KjernNo/specter/hardware/SPECTER.kicad_sch

## KiCad design hardware/SPECTER.kicad_sch (2026-04-02)

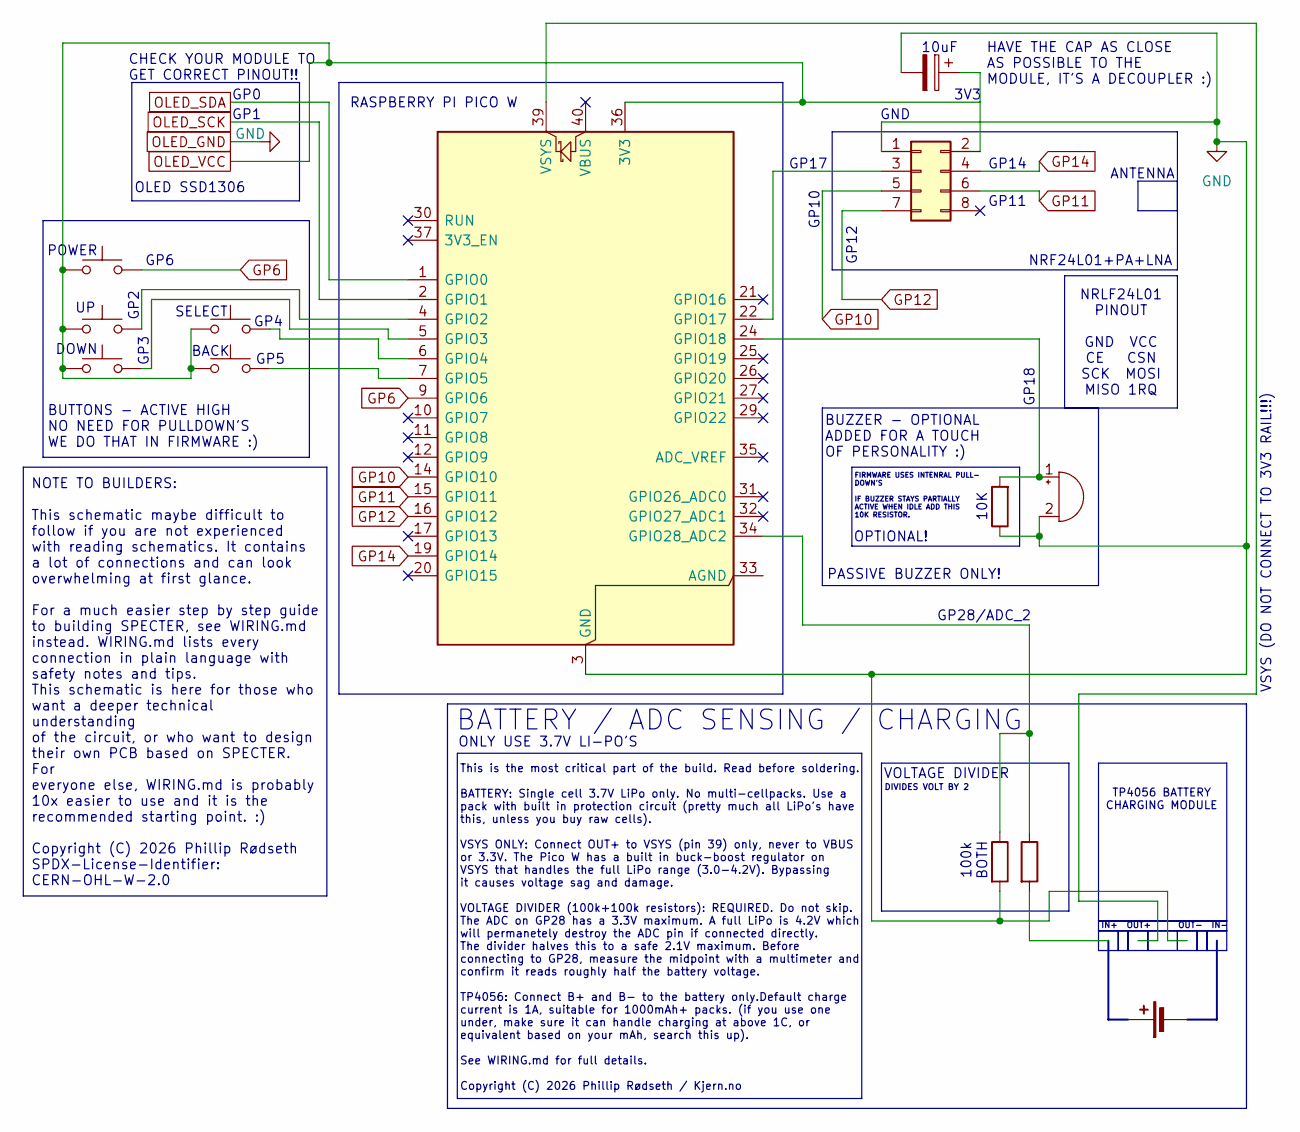
[picture p2: schematic SPECTER.kicad_sch]

Parts:
A1: RaspberryPi_Pico_W; RaspberryPi_Pico_W_SMD_HandSolder
BT1: Battery_Cell
BZ1: Buzzer
C1: C_Polarized
J1: Conn_02x04_Odd_Even
R1, R2, R3: R
SW1, SW2, SW3, SW4, SW5: SW_Push

Connections:
GND: A1.3 (GND), A1.8 (GND), A1.13 (GND), A1.18 (GND), A1.23 (GND), A1.28 (GND), A1.38 (GND), BZ1.2 (-), C1.2, J1.1, R1.1, R3.2
GP6: A1.9 (GPIO6), SW5.2
GP10: A1.14 (GPIO10), J1.5
GP11: A1.15 (GPIO11), J1.6
GP12: A1.16 (GPIO12), J1.7
GP14: A1.19 (GPIO14), J1.4
unnamed: A1.4 (GPIO2), SW3.2
unnamed: A1.5 (GPIO3), SW4.2
unnamed: A1.6 (GPIO4), SW1.2
unnamed: A1.7 (GPIO5), SW2.2
unnamed: A1.22 (GPIO17), J1.3
unnamed: A1.24 (GPIO18), BZ1.1 (+), R1.2
unnamed: A1.34 (GPIO28_ADC2), R2.1, R3.1
OLED_SCK: A1.2 (GPIO1)
OLED_SDA: A1.1 (GPIO0)
OLED_VCC: A1.36 (3V3), C1.1, J1.2, SW1.1, SW2.1, SW3.1, SW4.1, SW5.1

Notes on the sheet:
ANTENNA
VOLTAGE DIVIDER
OLED SSD1306
GP14
GP2
GP18
10uF
HAVE THE CAP AS CLOSE AS POSSIBLE TO THE MODULE, IT'S A DECOUPLER :)
DIVIDES VOLT BY 2
FIRMWARE USES INTENRAL PULL- DOWN'S IF BUZZER STAYS PARTIALLY ACTIVE WHEN IDLE ADD THIS 10K RESISTOR.
PASSIVE BUZZER ONLY!
RASPBERRY PI PICO W
BUTTONS - ACTIVE HIGH NO NEED FOR PULLDOWN'S WE DO THAT IN FIRMWARE :)
GP28/ADC_2
OPTIONAL!
GP1
GP5
This is the most critical part of the build. Read before soldering. BATTERY: Single cell 3.7V LiPo only. No multi-cellpacks. Use a pack with built in protection circuit (pretty much all LiPo's have this, unless you buy raw cells). VSYS ONLY: Connect OUT+ to VSYS (pin 39) only, never to VBUS or 3.3V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
100k BOTH
BATTERY / ADC SENSING / CHARGING
CHECK YOUR MODULE TO GET CORRECT PINOUT!!
VSYS (DO NOT CONNECT TO 3V3 RAIL!!!)
BACK
GP12
GP11
GP6
ONLY USE 3.7V LI-PO'S
GND
GP10
GP0
3V3
GP4
IN+ OUT+
OUT- IN-
GP17
GP3
POWER
TP4056 BATTERY CHARGING MODULE
NRF24L01+PA+LNA
SELECT
DOWN
10K
BUZZER - OPTIONAL ADDED FOR A TOUCH OF PERSONALITY :)
NOTE TO BUILDERS: This schematic maybe difficult to follow if you are not experienced with reading schematics. It contains a lot of connections and can look overwhelming at first glance. For a much easier step by step guide to building SPECTER, see WIRING.md instead. WIRING.md lists every connectio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
NRLF24L01 PINOUT GND VCC CE CSN SCK MOSI MISO 1RQ
